dennistgb/MAPP/lcd_utilities.cpp

/*
 * File:   lcd utilities.cpp
 *
 */
#undef __ARM_FP

#include "mbed.h"
#include "lcd.h"	// Include file is located in the project directory

#define DISPLAY_LCD_MASK 0x00000F00 //PORT A1: PA_15 : PA_8, 4-bit mode, using PA_11 : PA_8
#define DISPLAY_LCD_RESET 0x00000000

PortOut lcdPort(PortA, DISPLAY_LCD_MASK);
DigitalOut LCD_RS(PA_14);   //  Register Select on LC
DigitalOut LCD_EN(PA_12);   //  Enable on LCD controller
DigitalOut LCD_WR(PA_13);   //  Write on LCD controller

void lcd_strobe(void);

//--- Function for writing a command byte to the LCD in 4 bit mode -------------

void lcd_write_cmd(unsigned char cmd)
{
    unsigned char temp2;
    int tempLCDPort = 0;

    LCD_RS = 0;					// Select LCD for command mode
    wait_us(40);				// 40us delay for LCD to settle down
    temp2 = cmd;
    temp2 = temp2 >> 4;			// Output upper 4 bits, by shifting out lower 4 bits
    temp2 = temp2 & 0x0F;
                        		// Output to PORTD which is connected to LCD
    tempLCDPort = (int) temp2;
    tempLCDPort =  tempLCDPort << 8;
    tempLCDPort = tempLCDPort & 0x00000F00;
    lcdPort = tempLCDPort;


    wait_us(10000);			// 10ms - Delay at least 1 ms before strobing
    lcd_strobe();
    
	wait_us(10000);			// 10ms - Delay at least 1 ms after strobing

    temp2 = cmd;				// Re-initialise temp2 
    temp2 = temp2 & 0x0F;		// Mask out upper 4 bits
    
    tempLCDPort = (int) temp2;
    tempLCDPort =  tempLCDPort << 8;
    tempLCDPort = tempLCDPort & 0x00000F00;
    lcdPort = tempLCDPort;

    wait_us(10000);			// 10ms - Delay at least 1 ms before strobing
    lcd_strobe();
    wait_us(10000);			// 10ms - Delay at least 1 ms before strobing

}

//---- Function to write a character data to the LCD ---------------------------

void lcd_write_data(char data)
{
  	char temp1;
    int tempLCDPort = 0;

    LCD_RS = 1;					// Select LCD for data mode
    wait_us(40);				// 40us delay for LCD to settle down

    temp1 = data;
    temp1 = temp1 >> 4;
    temp1 = temp1 & 0x0F;

    tempLCDPort = (int) temp1;
    tempLCDPort =  tempLCDPort << 8;
    tempLCDPort = tempLCDPort & 0x00000F00;
    lcdPort = tempLCDPort;

	wait_us(10000); 
   	LCD_RS = 1;
    wait_us(10000);			//_-_ strobe data in

    lcd_strobe();
    wait_us(10000);

    temp1 = data;
    temp1 = temp1 & 0x0F;
    tempLCDPort = (int) temp1;  
    tempLCDPort =  tempLCDPort << 8;
    tempLCDPort = tempLCDPort & 0x00000F00;
    lcdPort = tempLCDPort;

    wait_us(10000);
	LCD_RS = 1;
    wait_us(10000); 			//_-_ strobe data in

    lcd_strobe();	
    wait_us(10000);
}


//-- Function to generate the strobe signal for command and character----------

void lcd_strobe(void)			// Generate the E pulse
{
    LCD_EN = 1;					// E = 0
    wait_us(10000);			// 10ms delay for LCD_EN to settle
    LCD_EN = 0;					// E = 1
    wait_us(10000);			// 10ms delay for LCD_EN to settle
}


//---- Function to initialise LCD module ----------------------------------------
void lcd_init(void)
{
    lcdPort = DISPLAY_LCD_RESET;				// lcd port (portA, PA8 - PA15) is connected to LCD data pin
    LCD_EN = 0;
    LCD_RS = 0;					// Select LCD for command mode
    LCD_WR = 0;					// Select LCD for write mode
   
    // Delay a total of 1 s for LCD module to
	// finish its own internal initialisation

    thread_sleep_for(1000);

    /* The data sheets warn that the LCD module may fail to initialise properly when
       power is first applied. This is particularly likely if the Vdd
       supply does not rise to its correct operating voltage quickly enough.

       It is recommended that after power is applied, a command sequence of
       3 bytes of 30h be sent to the module. This will ensure that the module is in
       8-bit mode and is properly initialised. Following this, the LCD module can be
       switched to 4-bit mode.
    */

    lcd_write_cmd(0x33);
    lcd_write_cmd(0x32);
      
    lcd_write_cmd(0x28);		// 001010xx � Function Set instruction
    							// DL=0 :4-bit interface,N=1 :2 lines,F=0 :5x7 dots
   
    lcd_write_cmd(0x0E);		// 00001110 � Display On/Off Control instruction
    							// D=1 :Display on,C=1 :Cursor on,B=0 :Cursor Blink on
   
    lcd_write_cmd(0x06);		// 00000110 � Entry Mode Set instruction
    							// I/D=1 :Increment Cursor position
   								// S=0 : No display shift
   
    lcd_write_cmd(0x01);		// 00000001 Clear Display instruction
 
    thread_sleep_for(20);			// 20 ms delay

}

void lcd_Clear(void)
{
    lcd_write_cmd(0x01);		// 00000001 Clear Display instruction
 
    thread_sleep_for(20);			// 20 ms delay

}

void lcd_write_string(const char *str) 
{
    while (*str) {
        lcd_write_data(*str); // Send each character to the LCD
        str++;                // Move to the next character
    }
}
